cvetaevvitaliy/Smart-Power-Case/HW/2020-05-31_0-52-48.png

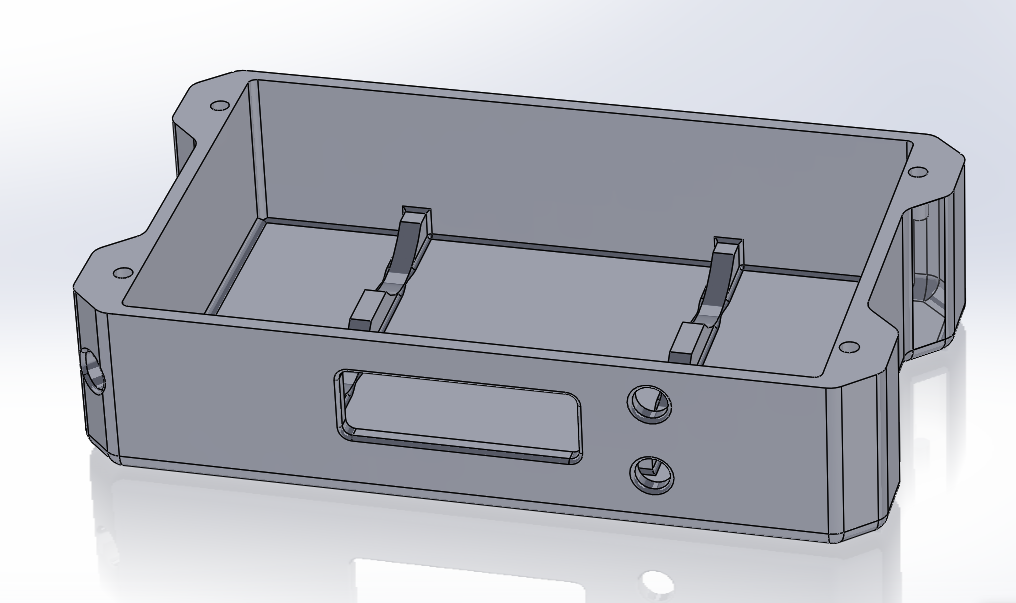
HW/2020-05-31_0-52-48.png
