cvetaevvitaliy/Smart-Power-Case/HW/2020-05-31_0-53-17.png

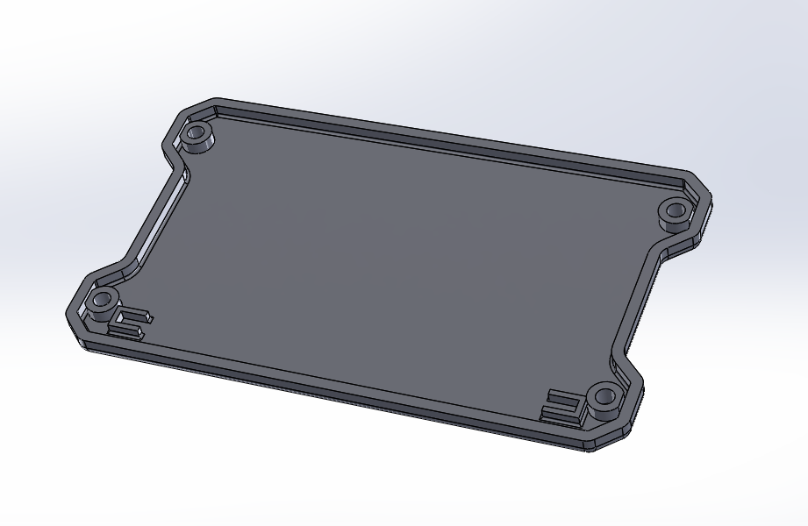
HW/2020-05-31_0-53-17.png
