cvetaevvitaliy/Smart-Power-Case/src/main_app/Debug.h

//
// Created by Vitaliy on 6/4/20.
//

#ifndef FATSHARK_POWER_V1_DEBUG_H
#define FATSHARK_POWER_V1_DEBUG_H
#include "main_app.h"

void Debug_Task(Device_Status_t *Data);

#endif //FATSHARK_POWER_V1_DEBUG_H
